ubx/Flaps_and_Speed_Display/doc/Brightness.png

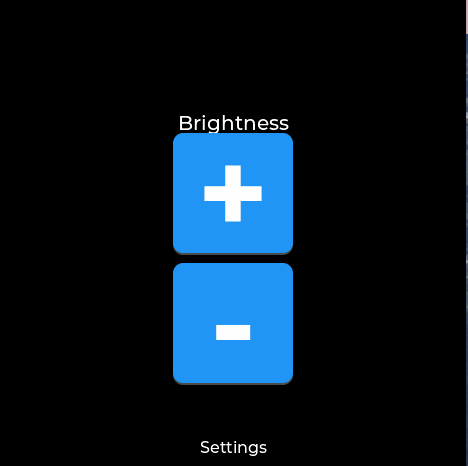
doc/Brightness.png
