ubx/Flaps_and_Speed_Display/doc/Flaps.png

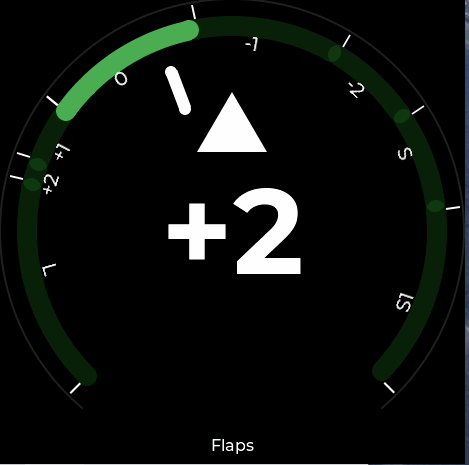
doc/Flaps.png
