ubx/Flaps_and_Speed_Display/doc/Polar_Files.png

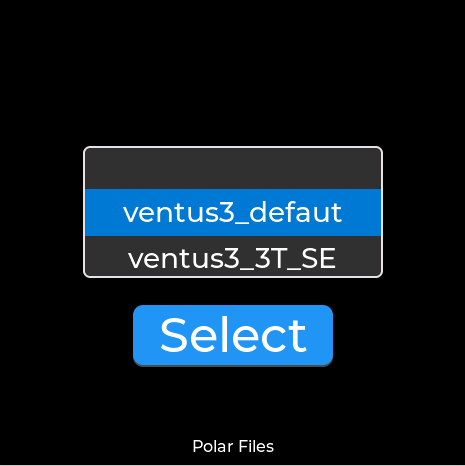
doc/Polar_Files.png
