ubx/Flaps_and_Speed_Display/src/ui/screens/screen6.cpp

#include <cmath>
#include "lvgl.h"
#include "../ui.h"
#include "../ui_helpers.hpp"

/* ================= CONFIG ================= */
#define WIND_MIN -180.0f
#define WIND_MAX 180.0f

#define NEEDLE_INNER_RADIUS 100
#define NEEDLE_OUTER_RADIUS 210

/* ================= STATE ================= */
static lv_obj_t* s_screen = nullptr;
static lv_obj_t* s_scale = nullptr;
static lv_obj_t* s_needle = nullptr;
static lv_obj_t* s_label = nullptr;
static lv_obj_t* s_inner_circle = nullptr;
static StaleOverlayState s_stale_overlay;

static lv_point_precise_t s_needle_pts[4];

extern const lv_font_t mono_digits_120;

/* ================= UTILS ================= */
static inline void make_noninteractive(lv_obj_t* o)
{
    if (!o) return;
    lv_obj_remove_flag(o, LV_OBJ_FLAG_CLICKABLE);
    lv_obj_remove_flag(o, LV_OBJ_FLAG_SCROLLABLE);
}

/* ================= DRAW NEEDLE ================= */
static void needle_draw_event(lv_event_t* e)
{
    lv_obj_t* obj = lv_event_get_target_obj(e);
    lv_layer_t* layer = lv_event_get_layer(e);

    lv_area_t coords;
    lv_obj_get_coords(obj, &coords);

    lv_point_precise_t p[4];

    for (int i = 0; i < 4; i++)
    {
        p[i].x = s_needle_pts[i].x + coords.x1;
        p[i].y = s_needle_pts[i].y + coords.y1;
    }

    /* ===== Fill (main color) ===== */
    lv_draw_triangle_dsc_t fill_dsc;
    lv_draw_triangle_dsc_init(&fill_dsc);

    fill_dsc.color = lv_palette_main(LV_PALETTE_BLUE);
    fill_dsc.opa = LV_OPA_COVER;

    // First triangle: tip, corner1, base_center
    fill_dsc.p[0] = p[0];
    fill_dsc.p[1] = p[1];
    fill_dsc.p[2] = p[2];
    lv_draw_triangle(layer, &fill_dsc);

    // Second triangle: tip, base_center, corner2
    fill_dsc.p[0] = p[0];
    fill_dsc.p[1] = p[2];
    fill_dsc.p[2] = p[3];
    lv_draw_triangle(layer, &fill_dsc);

    /* ===== Soft outline (anti-alias effect) ===== */
    lv_draw_line_dsc_t line_dsc;
    lv_draw_line_dsc_init(&line_dsc);

    line_dsc.color = lv_color_white();
    line_dsc.width = 2;
    line_dsc.opa   = LV_OPA_60;

    for (int i = 0; i < 4; i++)
    {
        line_dsc.p1 = p[i];
        line_dsc.p2 = p[(i + 1) % 4];
        lv_draw_line(layer, &line_dsc);
    }
}

/* ================= NEEDLE GEOMETRY ================= */
static void ui_set_needle_value(lv_obj_t* scale_obj,
                                lv_obj_t* needle_obj,
                                const int32_t inner_length,
                                const int32_t outer_length,
                                int32_t value,
                                float wind_speed)
{
    lv_obj_align(needle_obj, LV_ALIGN_TOP_LEFT, 0, 0);

    int32_t rotation = lv_scale_get_rotation(scale_obj);
    int32_t angle_range = lv_scale_get_angle_range(scale_obj);
    int32_t min = lv_scale_get_range_min_value(scale_obj);
    int32_t max = lv_scale_get_range_max_value(scale_obj);
    int32_t width = lv_obj_get_width(scale_obj);
    int32_t height = lv_obj_get_height(scale_obj);

    int32_t angle = 0;
    if (value > min)
    {
        if (value > max) angle = angle_range;
        else angle = (int32_t)((int64_t)angle_range * (value - min) / (max - min));
    }

    int32_t total_angle = rotation + angle;

    /* ===== Improved arrow geometry, scaled by wind speed ===== */
    // Base dimensions for a wind speed of 20 km/h (approx)
    // We'll scale from 0.4x (at 0 km/h) to 2.5x (at 100 km/h)
    float scale = 0.4f + (wind_speed / 40.0f); // 20 km/h is 0.9x, 40 km/h is 1.4x, etc.
    if (scale < 0.4f) scale = 0.4f;
    if (scale > 2.5f) scale = 2.5f;

    const int32_t head_length = (int32_t)(50.0f * scale);
    const int32_t head_width  = (int32_t)(30.0f * scale);
    const int32_t indent_len  = (int32_t)(15.0f * scale);

    int32_t cos_a = lv_trigo_cos(total_angle);
    int32_t sin_a = lv_trigo_sin(total_angle);

    int32_t cos_p = lv_trigo_cos(total_angle + 90);
    int32_t sin_p = lv_trigo_sin(total_angle + 90);

    /* Point 0: Tip (inner ring) */
    s_needle_pts[0].x = (width / 2) + ((inner_length * cos_a) >> LV_TRIGO_SHIFT);
    s_needle_pts[0].y = (height / 2) + ((inner_length * sin_a) >> LV_TRIGO_SHIFT);

    /* Point 1: Corner Left (base) */
    s_needle_pts[1].x = (width / 2)
        + (((inner_length + head_length) * cos_a) >> LV_TRIGO_SHIFT)
        + ((head_width * cos_p) >> LV_TRIGO_SHIFT);

    s_needle_pts[1].y = (height / 2)
        + (((inner_length + head_length) * sin_a) >> LV_TRIGO_SHIFT)
        + ((head_width * sin_p) >> LV_TRIGO_SHIFT);

    /* Point 2: Indented base center */
    s_needle_pts[2].x = (width / 2)
        + (((inner_length + head_length - indent_len) * cos_a) >> LV_TRIGO_SHIFT);

    s_needle_pts[2].y = (height / 2)
        + (((inner_length + head_length - indent_len) * sin_a) >> LV_TRIGO_SHIFT);

    /* Point 3: Corner Right (base) */
    s_needle_pts[3].x = (width / 2)
        + (((inner_length + head_length) * cos_a) >> LV_TRIGO_SHIFT)
        - ((head_width * cos_p) >> LV_TRIGO_SHIFT);

    s_needle_pts[3].y = (height / 2)
        + (((inner_length + head_length) * sin_a) >> LV_TRIGO_SHIFT)
        - ((head_width * sin_p) >> LV_TRIGO_SHIFT);

    lv_obj_invalidate(needle_obj);
}

/* ================= GAUGE ================= */
static void ui_create_gauge()
{
    s_screen = lv_obj_create(nullptr);
    lv_obj_set_style_bg_color(s_screen, lv_color_black(), 0);
    lv_obj_set_style_bg_opa(s_screen, LV_OPA_COVER, 0);

    s_scale = lv_scale_create(s_screen);
    lv_obj_set_size(s_scale, 466, 466);
    lv_obj_center(s_scale);

    lv_scale_set_mode(s_scale, LV_SCALE_MODE_ROUND_INNER);
    lv_scale_set_range(s_scale, (int32_t)WIND_MIN, (int32_t)WIND_MAX);
    lv_scale_set_total_tick_count(s_scale, 37);
    lv_scale_set_major_tick_every(s_scale, 3);
    lv_scale_set_angle_range(s_scale, 360);
    lv_scale_set_rotation(s_scale, 90);
    lv_scale_set_label_show(s_scale, true);

    lv_obj_set_style_text_color(s_scale, lv_color_white(), 0);
    lv_obj_set_style_text_font(s_scale, &lv_font_montserrat_20, 0);

    /* Needle object */
    s_needle = lv_obj_create(s_scale);
    lv_obj_remove_style_all(s_needle);
    lv_obj_set_size(s_needle, lv_pct(100), lv_pct(100));
    make_noninteractive(s_needle);
    lv_obj_add_event_cb(s_needle, needle_draw_event, LV_EVENT_DRAW_MAIN, nullptr);

    /* Inner circle */
    s_inner_circle = lv_obj_create(s_screen);
    lv_obj_set_size(s_inner_circle, NEEDLE_INNER_RADIUS * 2, NEEDLE_INNER_RADIUS * 2);
    lv_obj_center(s_inner_circle);
    lv_obj_set_style_radius(s_inner_circle, LV_RADIUS_CIRCLE, 0);
    lv_obj_set_style_bg_opa(s_inner_circle, LV_OPA_0, 0);
    lv_obj_set_style_border_color(s_inner_circle, lv_color_white(), 0);
    lv_obj_set_style_border_width(s_inner_circle, 4, 0);
    make_noninteractive(s_inner_circle);

    /* Label */
    s_label = lv_label_create(s_screen);
    lv_obj_set_style_text_color(s_label, lv_color_white(), 0);
    lv_obj_set_style_text_font(s_label, &mono_digits_120, 0);
    lv_label_set_text(s_label, "--");
    lv_obj_center(s_label);

    /* Unit */
    lv_obj_t* unit = lv_label_create(s_screen);
    lv_obj_set_style_text_color(unit, lv_color_white(), 0);
    lv_obj_set_style_text_font(unit, &lv_font_montserrat_16, 0);
    lv_label_set_text(unit, "km/h");
    lv_obj_align(unit, LV_ALIGN_CENTER, 0, 80);

    /* Title */
    lv_obj_t* title = lv_label_create(s_screen);
    make_noninteractive(title);
    lv_label_set_text(title, "Wind");
    lv_obj_set_style_text_color(title, lv_color_white(), 0);
    lv_obj_set_style_text_font(title, &lv_font_montserrat_16, 0);
    lv_obj_set_style_bg_color(title, lv_color_black(), 0);
    lv_obj_set_style_bg_opa(title, LV_OPA_COVER, 0);
    lv_obj_align(title, LV_ALIGN_BOTTOM_MID, 0, -10);

    ui_set_needle_value(s_scale, s_needle,
                        NEEDLE_INNER_RADIUS,
                        NEEDLE_OUTER_RADIUS,
                        0,
                        0.0f);

    s_stale_overlay = {};
}

/* ================= TIMER ================= */
static void ui_update_timer_cb(lv_timer_t*)
{
    if (lv_screen_active() != s_screen) return;

    const bool stale = is_stale();
    ui_set_stale_overlay(s_screen, s_stale_overlay, stale);

    float wind_speed = get_wind_speed_kmh();
    float wind_dir = get_wind_direction();
    float heading = get_heading();

    float rel_dir = wind_dir - heading + 180.0f;
    while (rel_dir > 180.0f) rel_dir -= 360.0f;
    while (rel_dir < -180.0f) rel_dir += 360.0f;

    static float s_smoothed_rel_dir = 0.0f;
    static bool s_first_run = true;

    if (s_first_run)
    {
        s_smoothed_rel_dir = rel_dir;
        s_first_run = false;
    }
    else
    {
        float diff = rel_dir - s_smoothed_rel_dir;
        while (diff > 180.0f) diff -= 360.0f;
        while (diff < -180.0f) diff += 360.0f;

        s_smoothed_rel_dir += diff * 0.15f;

        while (s_smoothed_rel_dir > 180.0f) s_smoothed_rel_dir -= 360.0f;
        while (s_smoothed_rel_dir < -180.0f) s_smoothed_rel_dir += 360.0f;
    }

    ui_set_needle_value(s_scale, s_needle,
                        NEEDLE_INNER_RADIUS,
                        NEEDLE_OUTER_RADIUS,
                        (int32_t)lroundf(s_smoothed_rel_dir),
                        wind_speed);

    static uint8_t div = 0;
    if (++div >= 5)
    {
        div = 0;
        lv_label_set_text_fmt(s_label, "%d", (int)lroundf(wind_speed));
    }
}

/* ================= PUBLIC ================= */
void screen6_create()
{
    ui_create_gauge();
    lv_timer_create(ui_update_timer_cb, 40, nullptr);
}

lv_obj_t* screen6_get()
{
    return s_screen;
}
