ubx/Flaps_and_Speed_Display/src/ui/screens/screen4.cpp

#include "lvgl.h"
#include "../ui.h"
#include "../ui_helpers.hpp"
#include "flaputils.hpp"
#include <cstdio>
#include <string>

static lv_obj_t* s_screen = nullptr;
static lv_obj_t* s_label_ias = nullptr;
static lv_obj_t* s_label_weight = nullptr;
static lv_obj_t* s_label_flap_actual = nullptr;
static lv_obj_t* s_label_flap_target = nullptr;
static lv_obj_t* s_label_alt = nullptr;
static lv_obj_t* s_label_heading = nullptr;
static lv_obj_t* s_label_wind = nullptr;
static lv_obj_t* s_label_gps_ground_speed = nullptr;
static lv_obj_t* s_label_gps_true_track = nullptr;
static lv_obj_t* s_label_polar = nullptr;
static StaleOverlayState s_stale_overlay;


static void ui_update_timer_cb(lv_timer_t* timer)
{
    if (!s_screen || lv_screen_active() != s_screen) return;
    ui_set_stale_overlay(s_screen, s_stale_overlay, is_stale());

    char buf[64];

    // IAS
    snprintf(buf, sizeof(buf), "IAS: %.0f km/h", get_ias_kmh());
    lv_label_set_text(s_label_ias, buf);

    // Weight
    snprintf(buf, sizeof(buf), "Weight: %.0f kg", get_weight_kg());
    lv_label_set_text(s_label_weight, buf);

    // Flap Actual
    flaputils::FlapSymbolResult actual = get_flap_actual();
    const char* actual_name = flaputils::get_flap_symbol_name(actual.index);
    snprintf(buf, sizeof(buf), "Flap Actual: %s (%d)", actual_name ? actual_name : "---", actual.index);
    lv_label_set_text(s_label_flap_actual, buf);

    // Flap Target
    flaputils::FlapSymbolResult target = get_flap_target();
    const char* target_name = flaputils::get_flap_symbol_name(target.index);
    snprintf(buf, sizeof(buf), "Flap Target: %s (%d)", target_name ? target_name : "---", target.index);
    lv_label_set_text(s_label_flap_target, buf);

    // Alt
    snprintf(buf, sizeof(buf), "Alt: %.0f m", get_alt_m());
    lv_label_set_text(s_label_alt, buf);

    // Heading
    snprintf(buf, sizeof(buf), "HDG: %.0f deg", get_heading());
    lv_label_set_text(s_label_heading, buf);

    // Wind
    snprintf(buf, sizeof(buf), "Wind: %.0f km/h @ %.0f deg", get_wind_speed_kmh(), get_wind_direction());
    lv_label_set_text(s_label_wind, buf);

    // GPS Ground Speed
    snprintf(buf, sizeof(buf), "GS: %.0f km/h", get_gps_ground_speed_kmh());
    lv_label_set_text(s_label_gps_ground_speed, buf);

    // GPS True Track
    snprintf(buf, sizeof(buf), "TRK: %.0f deg", get_gps_true_track());
    lv_label_set_text(s_label_gps_true_track, buf);

    // Polar
    std::string polar_name = flaputils::get_polar();
    size_t last_dot = polar_name.find_last_of('.');
    if (last_dot != std::string::npos) {
        polar_name = polar_name.substr(0, last_dot);
    }
    snprintf(buf, sizeof(buf), "Polar: %s", polar_name.c_str());
    lv_label_set_text(s_label_polar, buf);
}

void screen4_create()
{
    s_screen = lv_obj_create(nullptr);
    lv_obj_set_style_bg_color(s_screen, lv_color_black(), 0);
    lv_obj_set_style_bg_opa(s_screen, LV_OPA_COVER, 0);

    lv_obj_t* title = lv_label_create(s_screen);
    lv_label_set_text(title, "Live Params");
    lv_obj_set_style_text_color(title, lv_color_white(), 0);
    lv_obj_set_style_text_font(title, &lv_font_montserrat_16, 0);
    lv_obj_align(title, LV_ALIGN_BOTTOM_MID, 0, -10);

    s_label_ias = lv_label_create(s_screen);
    lv_obj_set_style_text_color(s_label_ias, lv_color_white(), 0);
    lv_obj_set_style_text_font(s_label_ias, &lv_font_montserrat_20, 0);
    lv_obj_align(s_label_ias, LV_ALIGN_TOP_MID, 0, 10);

    s_label_weight = lv_label_create(s_screen);
    lv_obj_set_style_text_color(s_label_weight, lv_color_white(), 0);
    lv_obj_set_style_text_font(s_label_weight, &lv_font_montserrat_20, 0);
    lv_obj_align(s_label_weight, LV_ALIGN_TOP_MID, 0, 50);

    s_label_flap_actual = lv_label_create(s_screen);
    lv_obj_set_style_text_color(s_label_flap_actual, lv_color_white(), 0);
    lv_obj_set_style_text_font(s_label_flap_actual, &lv_font_montserrat_20, 0);
    lv_obj_align(s_label_flap_actual, LV_ALIGN_TOP_MID, 0, 90);

    s_label_flap_target = lv_label_create(s_screen);
    lv_obj_set_style_text_color(s_label_flap_target, lv_color_white(), 0);
    lv_obj_set_style_text_font(s_label_flap_target, &lv_font_montserrat_20, 0);
    lv_obj_align(s_label_flap_target, LV_ALIGN_TOP_MID, 0, 130);

    s_label_alt = lv_label_create(s_screen);
    lv_obj_set_style_text_color(s_label_alt, lv_color_white(), 0);
    lv_obj_set_style_text_font(s_label_alt, &lv_font_montserrat_20, 0);
    lv_obj_align(s_label_alt, LV_ALIGN_TOP_MID, 0, 170);

    s_label_heading = lv_label_create(s_screen);
    lv_obj_set_style_text_color(s_label_heading, lv_color_white(), 0);
    lv_obj_set_style_text_font(s_label_heading, &lv_font_montserrat_20, 0);
    lv_obj_align(s_label_heading, LV_ALIGN_TOP_MID, 0, 210);

    s_label_wind = lv_label_create(s_screen);
    lv_obj_set_style_text_color(s_label_wind, lv_color_white(), 0);
    lv_obj_set_style_text_font(s_label_wind, &lv_font_montserrat_20, 0);
    lv_obj_align(s_label_wind, LV_ALIGN_TOP_MID, 0, 250);

    s_label_gps_ground_speed = lv_label_create(s_screen);
    lv_obj_set_style_text_color(s_label_gps_ground_speed, lv_color_white(), 0);
    lv_obj_set_style_text_font(s_label_gps_ground_speed, &lv_font_montserrat_20, 0);
    lv_obj_align(s_label_gps_ground_speed, LV_ALIGN_TOP_MID, 0, 290);

    s_label_gps_true_track = lv_label_create(s_screen);
    lv_obj_set_style_text_color(s_label_gps_true_track, lv_color_white(), 0);
    lv_obj_set_style_text_font(s_label_gps_true_track, &lv_font_montserrat_20, 0);
    lv_obj_align(s_label_gps_true_track, LV_ALIGN_TOP_MID, 0, 330);

    s_label_polar = lv_label_create(s_screen);
    lv_obj_set_style_text_color(s_label_polar, lv_color_white(), 0);
    lv_obj_set_style_text_font(s_label_polar, &lv_font_montserrat_20, 0);
    lv_obj_align(s_label_polar, LV_ALIGN_TOP_MID, 0, 370);

    s_stale_overlay = {};

    lv_timer_create(ui_update_timer_cb, 500, nullptr);
}

lv_obj_t* screen4_get()
{
    return s_screen;
}
